wilsondr9999/1005-Flash-Programmer/Additional Files/32Mhz.png

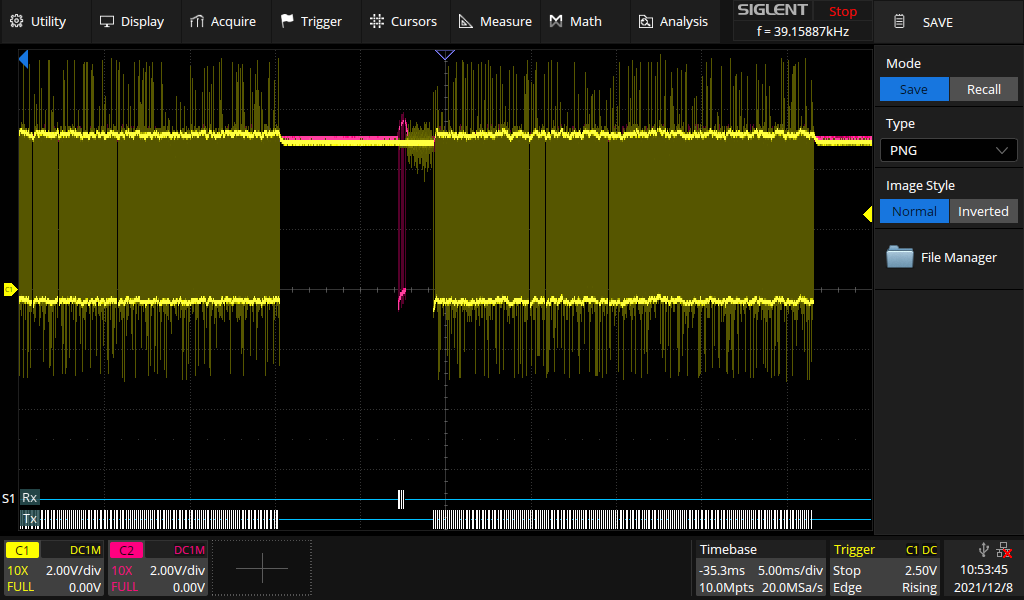
Additional Files/32Mhz.png
