wilsondr9999/1005-Flash-Programmer/Additional Files/ChipErase1.png

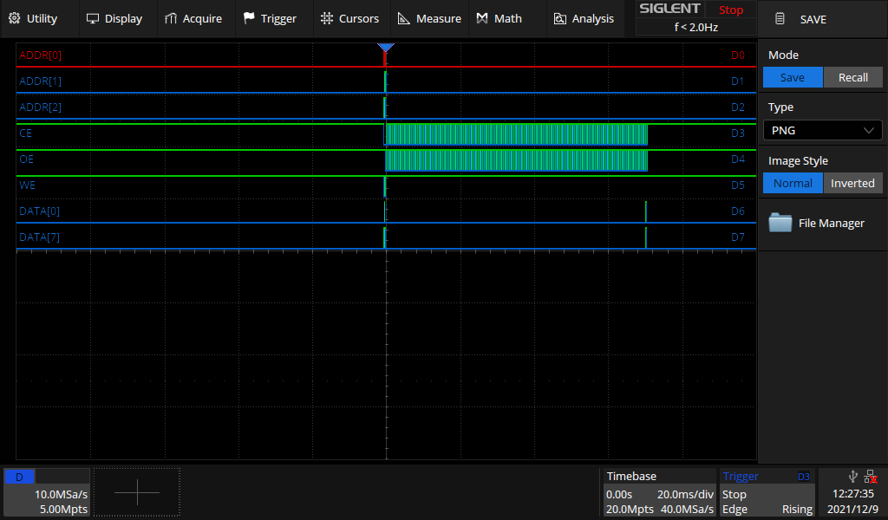
Additional Files/ChipErase1.png
