wilsondr9999/1005-Flash-Programmer/Additional Files/ChipErase2.png

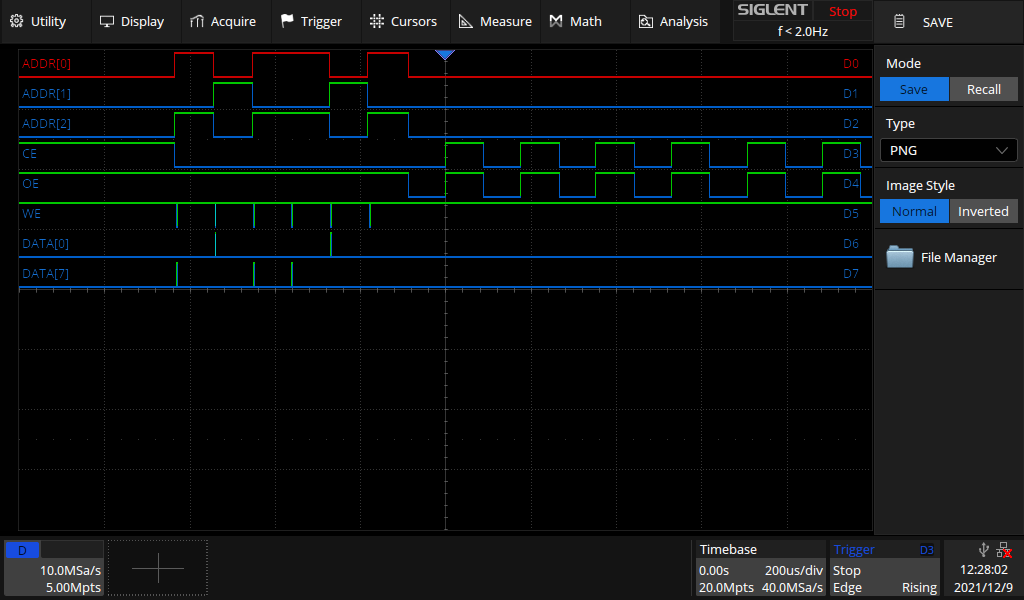
Additional Files/ChipErase2.png
