wilsondr9999/1005-Flash-Programmer/Additional Files/ChipErase3.png

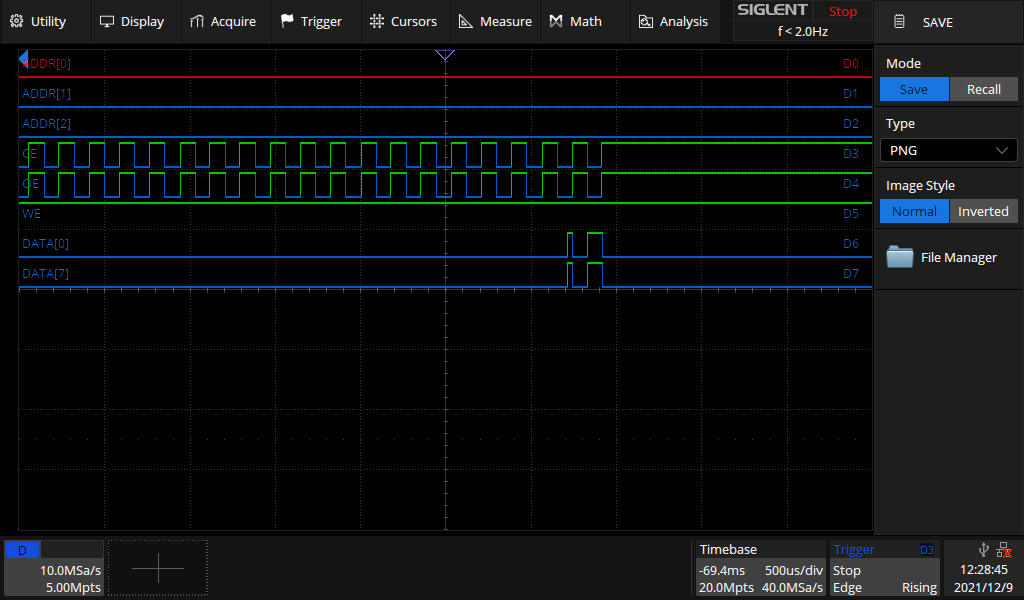
Additional Files/ChipErase3.png
