wilsondr9999/1005-Flash-Programmer/Additional Files/ChipID.png

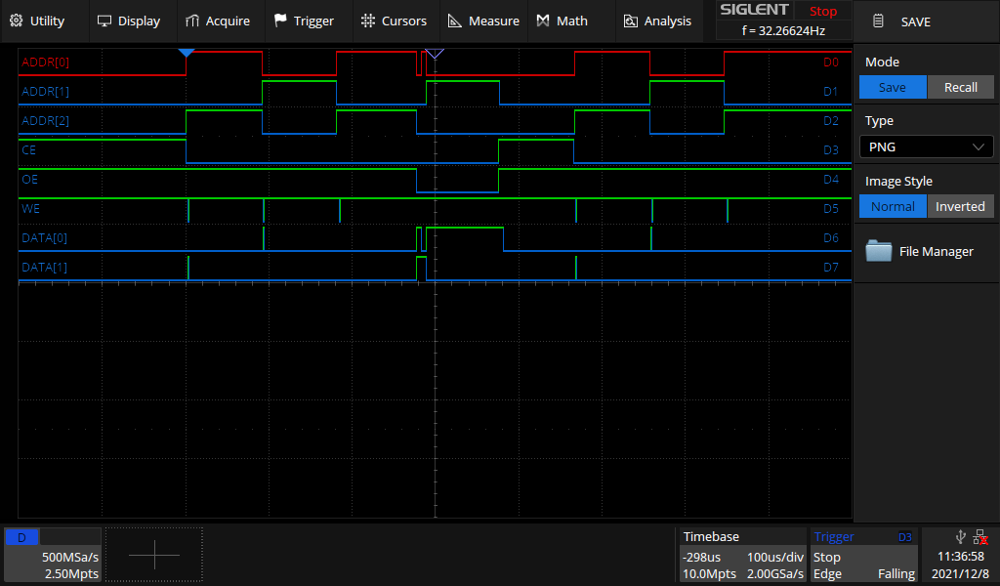
Additional Files/ChipID.png
