wilsondr9999/1005-Flash-Programmer/Additional Files/Write3.png

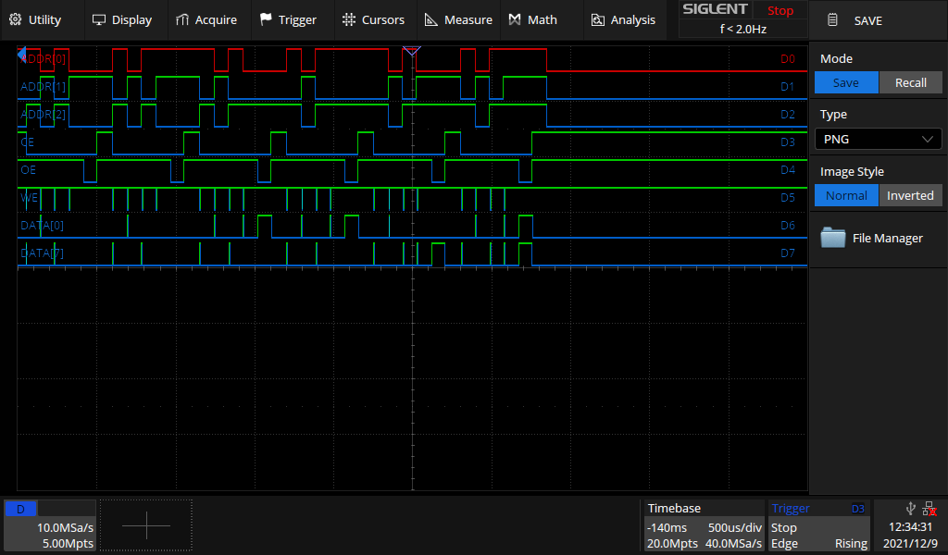
Additional Files/Write3.png
